ayaangrover/frost/frost/frost.kicad_sch

## KiCad design frost/frost.kicad_sch (2025-06-05)

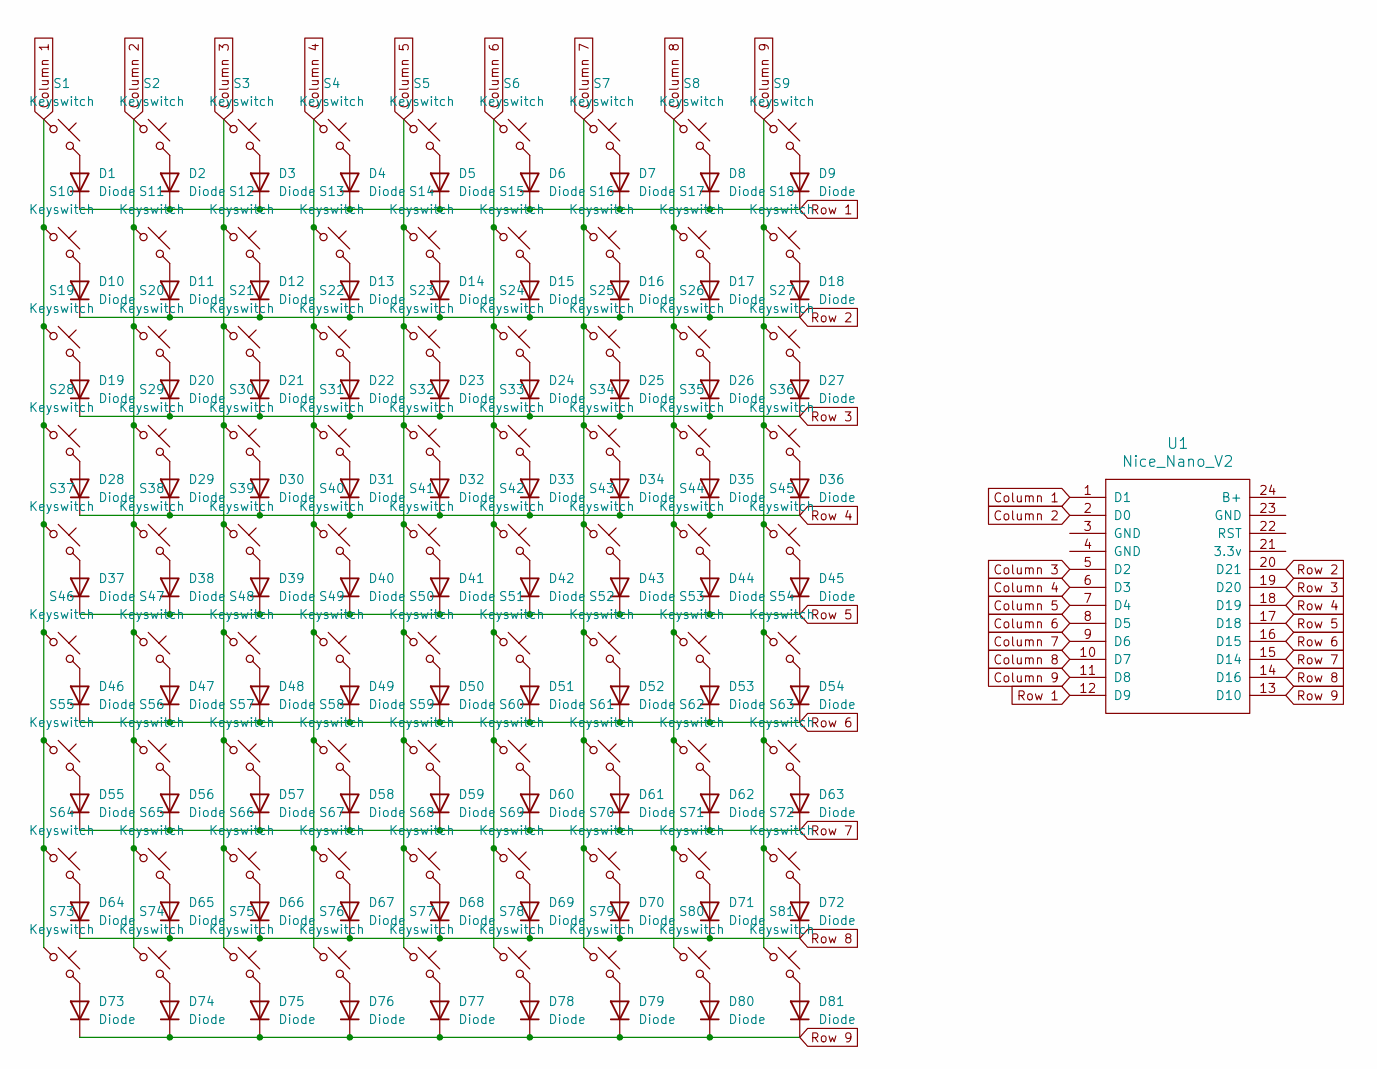
[picture p5: schematic frost.kicad_sch]

Parts:
D1, D2, D3, D4, D5, D6, D7, D8, D9, D10, D11, D12, D13, D14, D15, D16, D17, D18, D19, D20, D21, D22, D23, D24, D25, D26, D27, D28, D29, D30, D31, D32, D33, D34, D35, D36, D37, D38, D39, D40, D41, D42, D43, D44, D45, D46, D47, D48, D49, D50, D51, D52, D53, D54, D55, D56, D57, D58, D59, D60, D61, D62, D63, D64, D65, D66, D67, D68, D69, D70, D71, D72, D73, D74, D75, D76, D77, D78, D79, D80, D81: Diode; Diode_DO-35
S1, S2, S3, S4, S5, S6, S7, S8, S9, S10, S11, S12, S13, S14, S15, S16, S17, S18, S19, S20, S21, S22, S23, S24, S25, S26, S27, S28, S31, S32, S33, S34, S35, S36, S37, S38, S39, S40, S41, S42, S45, S46, S47, S48, S49, S50, S51, S52, S53, S54, S55, S57, S59, S60, S61, S62, S63, S64, S65, S66, S67, S68, S70, S71, S76, S77, S78, S79, S80, S81: Keyswitch; Hotswap_MX_1.00u
S29: Keyswitch; Hotswap_MX_2.00u
S30, S43: Keyswitch; Hotswap_MX_1.50u
S44, S69: Keyswitch; Hotswap_MX_1.75u
S56, S58: Keyswitch; Hotswap_MX_2.25u
S72, S73, S74: Keyswitch; Hotswap_MX_1.25u
S75: Keyswitch; Hotswap_MX_6.25u
U1: Nice_Nano_V2

Connections:
Column 1: S1.1, S10.1, S19.1, S28.1, S37.1, S46.1, S55.1, S64.1, S73.1, U1.1 (D1)
Column 2: S2.1, S11.1, S20.1, S29.1, S38.1, S47.1, S56.1, S65.1, S74.1, U1.2 (D0)
Column 3: S3.1, S12.1, S21.1, S30.1, S39.1, S48.1, S57.1, S66.1, S75.1, U1.5 (D2)
Column 4: S4.1, S13.1, S22.1, S31.1, S40.1, S49.1, S58.1, S67.1, S76.1, U1.6 (D3)
Column 5: S5.1, S14.1, S23.1, S32.1, S41.1, S50.1, S59.1, S68.1, S77.1, U1.7 (D4)
Column 6: S6.1, S15.1, S24.1, S33.1, S42.1, S51.1, S60.1, S69.1, S78.1, U1.8 (D5)
Column 7: S7.1, S16.1, S25.1, S34.1, S43.1, S52.1, S61.1, S70.1, S79.1, U1.9 (D6)
Column 8: S8.1, S17.1, S26.1, S35.1, S44.1, S53.1, S62.1, S71.1, S80.1, U1.10 (D7)
Column 9: S9.1, S18.1, S27.1, S36.1, S45.1, S54.1, S63.1, S72.1, S81.1, U1.11 (D8)
unnamed: D1.2 (A), S1.2
unnamed: D2.2 (A), S2.2
unnamed: D3.2 (A), S3.2
unnamed: D4.2 (A), S4.2
unnamed: D5.2 (A), S5.2
unnamed: D6.2 (A), S6.2
unnamed: D7.2 (A), S7.2
unnamed: D8.2 (A), S8.2
unnamed: D9.2 (A), S9.2
unnamed: D10.2 (A), S10.2
unnamed: D11.2 (A), S11.2
unnamed: D12.2 (A), S12.2
unnamed: D13.2 (A), S13.2
unnamed: D14.2 (A), S14.2
unnamed: D15.2 (A), S15.2
unnamed: D16.2 (A), S16.2
unnamed: D17.2 (A), S17.2
unnamed: D18.2 (A), S18.2
unnamed: D19.2 (A), S19.2
unnamed: D20.2 (A), S20.2
unnamed: D21.2 (A), S21.2
unnamed: D22.2 (A), S22.2
unnamed: D23.2 (A), S23.2
unnamed: D24.2 (A), S24.2
unnamed: D25.2 (A), S25.2
unnamed: D26.2 (A), S26.2
unnamed: D27.2 (A), S27.2
unnamed: D28.2 (A), S28.2
unnamed: D29.2 (A), S29.2
unnamed: D30.2 (A), S30.2
unnamed: D31.2 (A), S31.2
unnamed: D32.2 (A), S32.2
unnamed: D33.2 (A), S33.2
unnamed: D34.2 (A), S34.2
unnamed: D35.2 (A), S35.2
unnamed: D36.2 (A), S36.2
unnamed: D37.2 (A), S37.2
unnamed: D38.2 (A), S38.2
unnamed: D39.2 (A), S39.2
unnamed: D40.2 (A), S40.2
unnamed: D41.2 (A), S41.2
unnamed: D42.2 (A), S42.2
unnamed: D43.2 (A), S43.2
unnamed: D44.2 (A), S44.2
unnamed: D45.2 (A), S45.2
unnamed: D46.2 (A), S46.2
unnamed: D47.2 (A), S47.2
unnamed: D48.2 (A), S48.2
unnamed: D49.2 (A), S49.2
unnamed: D50.2 (A), S50.2
unnamed: D51.2 (A), S51.2
unnamed: D52.2 (A), S52.2
unnamed: D53.2 (A), S53.2
unnamed: D54.2 (A), S54.2
unnamed: D55.2 (A), S55.2
unnamed: D56.2 (A), S56.2
unnamed: D57.2 (A), S57.2
unnamed: D58.2 (A), S58.2
unnamed: D59.2 (A), S59.2
unnamed: D60.2 (A), S60.2
unnamed: D61.2 (A), S61.2
unnamed: D62.2 (A), S62.2
unnamed: D63.2 (A), S63.2
unnamed: D64.2 (A), S64.2
unnamed: D65.2 (A), S65.2
unnamed: D66.2 (A), S66.2
unnamed: D67.2 (A), S67.2
unnamed: D68.2 (A), S68.2
unnamed: D69.2 (A), S69.2
unnamed: D70.2 (A), S70.2
unnamed: D71.2 (A), S71.2
unnamed: D72.2 (A), S72.2
unnamed: D73.2 (A), S73.2
unnamed: D74.2 (A), S74.2
unnamed: D75.2 (A), S75.2
unnamed: D76.2 (A), S76.2
unnamed: D77.2 (A), S77.2
unnamed: D78.2 (A), S78.2
unnamed: D79.2 (A), S79.2
unnamed: D80.2 (A), S80.2
unnamed: D81.2 (A), S81.2
Row 1: D1.1 (K), D2.1 (K), D3.1 (K), D4.1 (K), D5.1 (K), D6.1 (K), D7.1 (K), D8.1 (K), D9.1 (K), U1.12 (D9)
Row 2: D10.1 (K), D11.1 (K), D12.1 (K), D13.1 (K), D14.1 (K), D15.1 (K), D16.1 (K), D17.1 (K), D18.1 (K), U1.20 (D21)
Row 3: D19.1 (K), D20.1 (K), D21.1 (K), D22.1 (K), D23.1 (K), D24.1 (K), D25.1 (K), D26.1 (K), D27.1 (K), U1.19 (D20)
Row 4: D28.1 (K), D29.1 (K), D30.1 (K), D31.1 (K), D32.1 (K), D33.1 (K), D34.1 (K), D35.1 (K), D36.1 (K), U1.18 (D19)
Row 5: D37.1 (K), D38.1 (K), D39.1 (K), D40.1 (K), D41.1 (K), D42.1 (K), D43.1 (K), D44.1 (K), D45.1 (K), U1.17 (D18)
Row 6: D46.1 (K), D47.1 (K), D48.1 (K), D49.1 (K), D50.1 (K), D51.1 (K), D52.1 (K), D53.1 (K), D54.1 (K), U1.16 (D15)
Row 7: D55.1 (K), D56.1 (K), D57.1 (K), D58.1 (K), D59.1 (K), D60.1 (K), D61.1 (K), D62.1 (K), D63.1 (K), U1.15 (D14)
Row 8: D64.1 (K), D65.1 (K), D66.1 (K), D67.1 (K), D68.1 (K), D69.1 (K), D70.1 (K), D71.1 (K), D72.1 (K), U1.14 (D16)
Row 9: D73.1 (K), D74.1 (K), D75.1 (K), D76.1 (K), D77.1 (K), D78.1 (K), D79.1 (K), D80.1 (K), D81.1 (K), U1.13 (D10)
